elijah-rou/PedalBoi/SPICE/prototype_1.asc

5V_In: voltage; 5
AudioBias: MCP6001
C1: cap; 10µF
C2: cap; 10µF
C3: cap; 10µF
InputBuffer: MCP6001
OutputBuffer: NJM4580
R1: res2; 100k
R2: res2; 100k
R3: res2; 2Meg
R4: res2; 2Meg
R5: res2; 2Meg
R6: res2; 2Meg
R7: res2; 2Meg
V1: voltage; wavefile=something.wav
Named nets: 0, Output
.trans 15
